ArnaudSchlumberger/PotaBoard/include/PotaData.h

#ifndef POTADATA_H
#define POTADATA_H
#include "Adafruit_BMP280.h"

//Collects and Sends Humidity Data from Sensors
void collectSendDataH();
//Collects and Sends Temperature and Pressure from BME280
void collectSendDataTP(Adafruit_BMP280 &bmp, float &temperature, float &pression);
//Sends Battery Voltage
void sendBatteryVoltage(const float batVoltage);


void collectDataHumidity(uint16_t &h1, uint16_t &h2, uint16_t &h3, uint16_t &h4);
void collectDataTempPress(Adafruit_BMP280 &bmp, float &temperature, float &pression);
#endif
